d-el/Nucci/LTspice/hvconv/hvconv.asc

C1: cap; 22n
C2: cap; 22n
C3: cap; 22n
D1: diode; 1SS400SM
D2: diode; 1SS400SM
D3: diode; 1SS400SM
Lp: ind2; 7µH; Rser=0.5 Cpar=0
Ls: ind2; 80µH; Rser=60 Cpar=0
M7: nmos; irlml0100
R1: res; 10000k
V1: voltage; 5
V12: voltage; PULSE(0 5 10u 0 0 1u 50u 100000)
Named nets: 0, +5V
.tran 0 10m 0 0.01 startup
.options abstol=1e-10
.options reltol=0.003
.inc irlml0100.lib
K  Lp  Ls  1
.inc 1SS370.lib
